Digital-Naturalism-Laboratories/Mothbox/docs/index.md

---
layout: default
title: Home
nav_order: 1
description: "The Mothbox is a low cost DIY insect monitor"
permalink: /
---

# Mothbox
The Mothbox is a low-cost, high-performance [insect monitor](https://digital-naturalism-laboratories.github.io/Mothbox/docs/about/specs/). It features a power efficient and lightweight design that helps field biologists deploy it in the depths of the jungle. Its low cost means you can deploy many devices to study a landscape or build one to study the biodiversity at your home!

All the physical designs, electronics schematics, Pi Scripts, and insect-IDing Artificial Intelligence are **provided free and open source**, so you can build, share, and improve on these designs yourself!

We currently offer designs for two different versions of the Mothbox now:
* [Mothbox Pro](https://digital-naturalism-laboratories.github.io/Mothbox/docs/building/mothbox_pro) - Factory Assembled electronics, easy to put together! (~$450 in parts)
* [Mothbox DIY](https://digital-naturalism-laboratories.github.io/Mothbox/docs/building/mothbox_diy) - Make a Mothbox entirely yourself with off-the-shelf parts! ($550 in parts)

We believe **studying insect biodiversity is integral to life on earth**, and simply want this technology in the hands of as many people as possible.

{: .important-title }
> Mailing List
>
> Are you interested in Mothboxing? Using it in the field? Building it? Please sign up for our mailing list to stay up to date with the latest features! **Email our rag-tag crew at INFO [ a t ] mothbox.org** with subject "Mothbox Mail."
>

{: .highlight }
Join our free [Mothbox CHAT GROUP](https://app.element.io/#/room/#mothbox:matrix.org)

{: .important-title }
> Mailing List
>
> Are you interested in Mothboxing? Using it in the field? Building it? Please sign up for our mailing list to stay up to date with the latest features! **Email our rag-tag crew at INFO [ a t ] mothbox.org** with subject "Mothbox Mail."
>
https://app.element.io/#/room/#mothbox:matrix.org

{: .important-title }
> Order Form
>
> If you want to get your hands on some new Mothboxes ASAP, [fill out our interest form](https://forms.gle/BnBhjBC4csW4BwTE7), and we will get back to you as soon as we can about how to get them to you!
>

See the [full specifications of what it can do here.](https://digital-naturalism-laboratories.github.io/Mothbox/docs/about/specs/)
Watch a [video presentation of our talk at the Smithsonian all about the Mothbox and its design.](https://www.youtube.com/watch?v=lZhh7ecnAgk)
or [read a scientific paper](https://besjournals.onlinelibrary.wiley.com/doi/10.1111/2041-210x.70327) about using a Mothbox!

PXL_20240720_054408351 MP-EDIT



## Why Study Insects for Conservation?
Insect populations can be used as an ultra high resolution sensor for changes in environments.

bafkreic4l337soddqseixdb4zy74mdmzqtg4g7v75toiondz2vouumwnlm-1

### Insects (Especially Moths and Beetles) are Hyperdiverse
Of all life on earth (including bacteria), there are about 2 million species scientists have described, and [half of all those species are insects!](https://ourworldindata.org/how-many-species-are-there#:~:text=In%20the%20chart%2C%20we%20see,reptiles%2C%20and%20over%206%2C000%20mammals.) What's more, if you look at **just moths,** there are about 144,000 species, meaning **about 1 in every 14 known species in the world is a moth!** For reference, there are only about 11,000 bird species, and only 6,500 species of mammals (and half are bats and rodents). 

Using creatures with a super diverse gene pool allows us to make sophisticated insights into the health of different areas. Combining the activity of thousands of species of insects with other data like climate, acoustic, or soil analysis, can provide deep analysis into how damaged environments can be repaired.

### Offer Highly Localized Insights
Because they tend to have short lives and often limited ranges, insects can provide super localized data. Moths, in particular, are great indicators of overall biodiversity, because they are often host-specific as caterpillars. This means they only feed on one or a limited number of plant species. So, by monitoring moths, you are getting proxy information about the local plant community.

For comparison, think about something like a jaguar. Jaguars are rarely spotted and scientifically valuable to see on a wildlife camera, but they have large ranges and long lives. The presence of a jaguar does not necessarily tell us much about the health of the specific environment where it was spotted. It could simply be travelling across disturbed farmland to escape from a destroyed habitat elsewhere, but this would not be an indicator that the disturbed farmland is healthy and safe for jaguars. 

Having an insect sensor (like a Mothbox) that compares the activity of thousands of different species of insects can highlight differences in environmental health in areas just a couple kilometers apart.

### They are Easy to Attract
Humans long ago discovered that many nocturnal insects like moths seem to be attracted to lights. We now know this is because [bright lights disorient their natural steering mechanism](https://www.nature.com/articles/s41467-024-44785-3). Scientists have used bright artificial lights for over a century to take censuses of insect populations. The problem with this type of "mothlighting" is that it can be incredibly time consuming, as a scientist has to hang out with the mothlight all night and note which insects are visiting. Instead we have an automated device that does all this work for you! You just deploy the Mothbox in the field, it runs while you're in the comfort of your own home, and you can collect it and analyze the data with AI when you're ready.

## What it Does

The Mothbox stays in an ultra low-power state until your schedule tells it which nights to wake up. Then it triggers an insect lure (usually a bright UV light) and takes ultra-high resolution photos of the visitors it attracts. 

PXL_20240607_025924783 NIGHT-EDIT

Next we created some open-source AI scripts that process the insect data for you. First, a trained YOLO v8 detects where all the insects are in the images and crops them out. This means that you can view just the cropped photos of insects instead of having to look through all the raw photo data.




Then we use BioCLIP via the [pybioclip](https://github.com/Imageomics/pybioclip) package, with a [FiftyOne](https://github.com/voxel51/fiftyone) user interface, to help you automatically group and ID the insects to different taxonomic levels!



# Build it Yourself!
PXL_20240810_155421647 MP

This Mothbox documentation will provide you with information on how to source, build, program, and use your Mothbox!

[Get started building your mothbox!](https://digital-naturalism-laboratories.github.io/Mothbox/docs/building)

After following these guides, you should be able to make your own set of Mothboxes to conduct your own biodiversity studies!




# Mothbeam
We are also building an open-source, portable, low-cost light for mothlighting, the Mothbeam! Some early documentation for [making your own Mothbeam is here.](https://mothbox.org/docs/building/mothbeam)


PXL_20240718_190826331 MP
