Digital-Naturalism-Laboratories/Mothbox/docs/docs/about/Acknowledgements.md

---
layout: default
title: Acknowledgements
parent: About the Mothbox
has_children: false
nav_order: 9
---
# Development Team

The Mothbox was originally developed by a core team of Andy Quitmeyer, Hubert Szczgiel, and Kitty Quitmeyer

* Andy Quitmeyer

Dr. Andy Quitmeyer designs new ways to interact with the natural world. Quitmeyer has worked with large organizations like Cartoon Network, IDEO, and the Smithsonian, taught as a tenure-track professor, and even had his research turned into a (silly) television series called “Hacking the Wild." distributed by Discovery Networks.

He spends most of his time volunteering with smaller organizations and communities, and co-founded the field-station/makerspace, [Digital Naturalism Laboratories](https://www.dinalab.net/). In the rainforest of Gamboa, Panama, Dinalab blends biological fieldwork and technological crafting with a community of local and international scientists, artists and engineers. 

* Hubert Szczygiel

Hubert Szczygiel is a tropical ecologist specializing in scalable biodiversity monitoring. Hubert has worked with the Smithsonian Tropical Research Institute since 2016. His current research pairs broad-spectrum biodiversity monitoring with new financial tools to enable reforestation. His research inspired the development of the original Mothbox.

* Kit Quitmeyer

Kit Quitmeyer is the Co-founder of [Dinalab](https://www.dinalab.net/), and lead technician of the protoyping facilities. With the Mothbox she has been the head of manufacturing operations and software training. She is a skilled craftsperson passionate about endangered animals, books, activism, and the environment. She works weekly at the [APPC animal rescue in Panama](https://www.appcpanama.org/who-we-are.html), and raises funds with her crafts to support them.

* Bri Johns

Bri Johns is an open science hardware researcher. After her role steering the Gathering for Open Science Hardware group as the community manager, she joined the Mothbox team as a research fellow working on the construction, deployment, and community access for the tool.

# Acknowledgements
The Mothbox has been made possibly with help from many individuals and groups like 

## Funding
* Wildlabs.net
* ARM
* The American Museum of Natural History
* Experiment.com
* Phoebe Zarnetske and the Michigan X-prize group

## Institutional Support

* [IVADO Institute](https://ivado.ca/)
  * Sponsored a collaboration with us and [Antenna](https://antenna.insectai.org) software for processing bugs
* Autodesk Foundation (Software Donation)
* University of Washington (Project Storage Space)

## Additional Support

* Pro-Eco Azuero
* Ponterra

* Daisy Dent
* Yash Sondhi
* Owen Mcmillan
* Sol Parra Santos

* [Craig Durkin](https://wandrer.earth/) set up this documentation site backend for us

* Christopher Lawrence
* GOSH community openhardware.science
* Lee Wilkins
* Julian Stirling
* Wildlives Rhode Island group
* Matt Flagg

* David Rolnick's lab and the [Antenna](https://antenna.insectai.org) crew

* Totumas Crew
 * Jessie Tejara-Fabian
 * Jeff Dietrich
 * Mulget Amaru
* [BeetlePalooza](https://doi.org/10.5281/zenodo.15272136) (Sponsored by the [Imageomics Institute](https://imageomics.org/) at The Ohio State University)
* [Bucket of Bugs](https://github.com/Digital-Naturalism-Laboratories/bucket-o-bugs) BeetlePalooza group
  * Elizabeth Campolongo, Ernie Parke, Andy Quitmeyer, Matt Thompson
* The McGuire Center for Lepidoptery

* Epaper Display Font help:
  * Logan Williams and Linotype Pilgrim 

* PCB Assistance
  * Paul Parkview 
  * Josh Muffin
  * Joel Murphy

* [TroubleMaker Shenzhen](https://troublemaker.site/)
  * Henk, Terry, and Ming
