Digital-Naturalism-Laboratories/Mothbox/docs/docs/processing/index.md

---
layout: default
title: Refining Data
nav_order: 4
has_children: true
permalink: /docs/processing
---
Have you been using the Mothbox, and now you have thousands of photos of cool bugs!? Want to do neat things with all these photos to turn them into interesting and beautiful data? We built a suite of open source scripts that we call the "Mothbot" for Mothbox! Check them all out!

There are two stages we go through to turn all our raw data into useful insights. We group them into

* Process - Mostly automated steps turning source images into labeled sub images
  * image(3)

* Classify - Augmented Human validation of insect data
  * image(4)
