Digital-Naturalism-Laboratories/Mothbox/docs/docs/previousversions/v3.21/3.21.md

---
layout: default
title: v3.21
nav_order: 9
has_children: true
permalink: /docs/previousversions/v3.21

---

# v3.21

This version was put into the field in April 2024. It features a pi 4 + pijuice + USB buck converter. It had multiple internal planes.
