Digital-Naturalism-Laboratories/Mothbox/docs/docs/processing/process/hacker/id.md

---
layout: default
title: Identify Detections
parent: Hacker Mode
has_children: false
nav_order: 4
---

## Using the Mothbot UI to ID Organisms

The next step in the data processing pipeline is to run a script that identifies all the organisms that were detected in the previous step. You can start by clicking on the tab that says "ID" towards the bottom of the UI. 

mothbotID1<br>

Once you've clicked this tab, you will notice a few new fields that pop up. The first field is the option to set the parameters for the taxonomic rank that the computer vision model ([BioCLIP](https://imageomics.github.io/bioclip/)) will use when identifying organisms (i.e. whether you want the model to identify your organisms to just the order level, or all the way down to the species level).

On the right side, you will see checkboxes to identify human and bot detections. You should leave both of these as true, as this will ensure every detection gets identified. You also have the option to override existing IDs if you would like by selecting the last checkbox.

MothbotID2<br>

Click the big orange box that says "Run Identification" and you will see the script running in the window below it.

MothbotID3<br>

> [!NOTE]
> When you first run the ID program with a specific species list, it needs to do a thing where it creates "embeddings" of that specific species list. They get saved as a ".pt" file next to your species list. This means the first time you run an ID, it might take a bit longer, but subsequent ID processing with the same species list should go faster! HOWEVER, there can be a time where, if you update that species list, you can get an error when you run the script because the old embeddings don't match that species list. so **if you get an error, delete that ".pt" file, and run it again**

When you are done running the ID script, your window should look like this (notice the green checkbox indicating that identifications are complete and text that says identification process is complete):

IDfinished<br>

## Next: Insert Metadata
Now that you have detected and identified your organisms, the next step is to make sure the metadata for your deployment is associated to your identified organisms. Head to the next step “[Insert Metadata](https://digital-naturalism-laboratories.github.io/Mothbox/docs/processing/process/hacker/insertmetadata/)” to continue.

## Run this Script Manually

The Python Script we use to run detections is called Mothbot_ID. This script tries to look at all your detected creatures and make a prediction as to what type of creature they are.

# Inputs
Like many of the other processing scripts, this program takes in several Inputs as default variables that you can change at the top of the file.


INPUT_PATH  - set this to the folder you want to ID (or a parent folder for a group of nights you want to ID).

SPECIES_LIST - path to a CSV file downloaded from GBIF's species list generator. For example, you could download this list of [only the insects that are in Panama](https://www.gbif.org/occurrence/taxonomy?country=PA&taxon_key=216). 

TAXONOMIC_RANK_FILTER=Rank.ORDER
This is the filter where you determine how deep you want the detections to go. The default is set to Rank.ORDER to try to determine what the ID of the creature is down to the ORDER level. You can change this all the way until Rank.SPECIES, but the accuracy of the AI model falls off the deeper you get. 
_Generally the Rank.ORDER or Rank.Family level are the most usuable settings_

# Results
The ID script can take 10-90 minutes depending on your computer speed and number of detections.

When you run the script, you will see it start processing your detections in each image.


It chooses a winning classification down to the taxonomic filter you specified (for example Order).
It saves this detection information into the .json files that you created when manually making detections or running the automated Detect script. (So you won't see any new files created.)

Now if you open your nightly folder in X-Anylabeling, you will see the labels no longer just say "creature" but rather list the taxonomic rank the script has predicted:





For editing and organizing these IDs into a dataset, we will go to the next step where we view all our results in an editable database.
