Digital-Naturalism-Laboratories/Mothbox/docs/docs/processing/process/hacker/insertExif.md

---
layout: default
title: Exif (Optional)
parent: Hacker Mode
has_children: false
nav_order: 7
---
# Launch Exif (Optional)

## Make Sure Exiftool is installed
There is a thing called "ExifTool" that (because exif data on images is super convoluted) needs to be installed to run CreateDataset


if you are using windows, you don't actually have to install it i think. It just points to a relatively positioned folder in the github that has the .exe it runs
if you are running mac or linux, you need to download exiftool (or the mac package .pkg is actually in in the AI folder of the github already for you as well)

## Insert EXIF Data Using Mothbot UI

We've created a script to insert EXIF data into each patch you've made, which is useful when you want to upload individual patches as photos to crowdsourcing platforms like iNaturalist. You can do this by clicking on the "Insert Exif" tab, then clicking the big orange button that says "Insert Exif"

exif1<br>

Once your script is running, it should look like this:

exif2<br>

And when it's finished, your window at the bottom should look like this:

exif3

You can now head to the next step, [Generating and Editing Datasets](https://digital-naturalism-laboratories.github.io/Mothbox/docs/processing/classify/)!
