Digital-Naturalism-Laboratories/Mothbox/docs/docs/about/index.md

---
layout: default
title: About the Mothbox
nav_order: 10
has_children: true
permalink: /docs/about
---

This is an open source science hardware and software project started by Andy Quitmeyer and Hubert Szczygiel in 2023. The goal is to provide people a low cost tool for insect biomonitoring they can build themselves from off the shelf parts. It aims to be low cost, high resolution, durable, and portable.

# Publications

You can read papers we published about the Mothbox here:

* [Methods in Ecology and Evolution](https://besjournals.onlinelibrary.wiley.com/doi/epdf/10.1111/2041-210x.70327) preprint [here](https://www.biorxiv.org/content/10.64898/2025.12.03.692171v2)
* [Integrative and Comparative Biology](https://academic.oup.com/icb/advance-article/doi/10.1093/icb/icag072/8700641?guestAccessKey=)

Here are some other papers published that talk about the Mothbox:

# Video Presentations
Here are some video presentations that discuss the motivations behind the Mothbox and its design:

Documentary about the Mothbox made for the Wildlabs Award:

<iframe width="560" height="315" src="https://www.youtube.com/watch?v=1LGz3aWpeVE&t=102s" title="Mothbox Wildlabs Documentary" frameborder="0" allow="accelerometer; autoplay; clipboard-write; encrypted-media; gyroscope; picture-in-picture; web-share" referrerpolicy="strict-origin-when-cross-origin" allowfullscreen></iframe>

Mothbox Invited Talk at the Smithsonian Tropical Research Institute (September 2024):
<iframe width="560" height="315" src="https://www.youtube.com/embed/lZhh7ecnAgk?si=vdF98dbD3mXoOiNE" title="YouTube video player" frameborder="0" allow="accelerometer; autoplay; clipboard-write; encrypted-media; gyroscope; picture-in-picture; web-share" referrerpolicy="strict-origin-when-cross-origin" allowfullscreen></iframe>

[Mothbox Symposium Keynote at Georgia Tech (October 2024)](https://research.gatech.edu/ipat/mothbox-lecture-oct29-2024)

[Mothbox Invited Seminar: “Expanding Horizons in Lepidoptera Research” McGuire Center Webinar Series ](https://ufl.zoom.us/rec/play/-Vr3mgX_anxGzv7Nv5OYsDCAKpSgtci48Wpri2sOOH7cdTbaxnvzdFAKVjW492BDWsz-Dkzi-UxSENHV.rh4Ph3Je4udUjZ9s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)
