Digital-Naturalism-Laboratories/Mothbox/docs/docs/processing/classify/index.md

---
layout: default
parent: Refining Data
title: Classification
nav_order: 8
has_children: true
permalink: /docs/processing/classify
---
During the classification step, we want to take automatically organized insect data and validate them with humans as quickly and accuratley as possible. We built our own program to let you do this in a quick and speedy way called "Classify."

* [Classify](https://mothbox.org/docs/processing/classify/classify/)

Note: we used to have an older version of this that used a fiftyone UI interface, but switched to this new homebrewed one we call "Classify" as it is much speedier and easier to use.
