Digital-Naturalism-Laboratories/Mothbox/docs/docs/processing/process/hacker/ui.md

---
layout: default
title: Start UI
parent: Hacker Mode
has_children: false
nav_order: 2
---
# Launch Mothbot_UI.py script

This script enables you to run all our post-processing scripts through a web application that runs locally on your computer. We were able to build this interactive user interface (UI) using [Gradio](https://github.com/gradio-app/gradio), an open source Python package that allows anyone to quickly build a web application for any sort of machine learning model or Python functions.  

## Make sure you have the latest version of the Mothbox Project on GitHub
Before running your post-processing scripts, it's important to make sure you have the most recent version of our scripts. You can do this by opening your GitHub desktop application and clicking "Fetch Origin" and then "Pull Origin." This will sync your local Mothbox folder with the repository that has the updated code. 

Github_Fetch<br>

Github_Pull<br>

>Note: if no changes have been made to our scripts, then you likely will not see an option to "Pull Origin" after you fetch it, as there will be nothing new for you to pull. 

Now that you've got the updated scripts, you can proceed with opening the Mothbox UI.

## Opening the UI Using Visual Studio Code

To get the UI running, you need to first open the Mothbot folder in Visual Studio Code. Start by opening your Visual Studio Code app, clicking File, then Open Folder, and opening the Mothbot Folder, which is within the AI folder of the Mothbox project (which can be found in your GitHub folder on your computer).

OpenFolder_VSC<br>
SelectMothbot<br>

You should then see the Mothbot folder appear in the sidebar in Visual Studio Code. Click on the dropdown, then select the Mothbot_UI.py script

mothbotUIinsidebar<br>

You will see the code pop up in the main window of Visual Studio Code, and all you have to do next is click the play button in the top right corner (aka Run Python File).

runpythonfile<br>

Next, the Mothbot UI should pop up as a web application that is running locally on your computer! 

mothbotAI<br>

## Start Detecting Bugs!
Now that you've got the UI running, you can start processing your data by detecting what critters are in your photos. Move on to the next step, Detect Creatures, to learn how!

## Running Scripts Manually
If you would like to run all of our Python scripts manually, we are including instructions on how to do so as part of each post-processing step listed on our site.
