Digital-Naturalism-Laboratories/Mothbox/AI/trained_models/train14_3000Images_batch2_1408px/train_batch67502.jpg

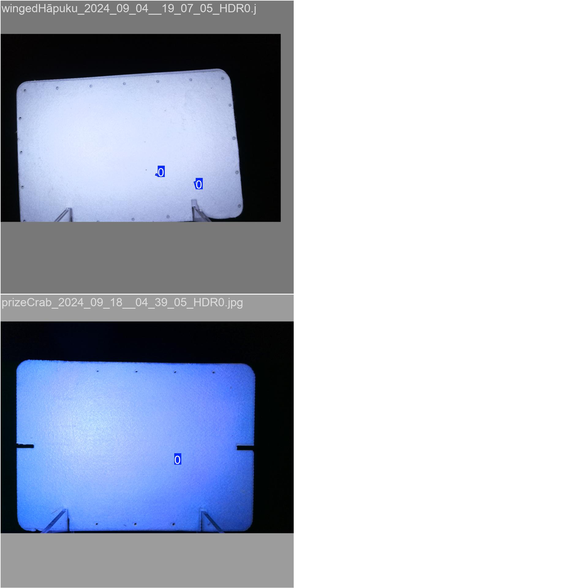
AI/trained_models/train14_3000Images_batch2_1408px/train_batch67502.jpg
