Digital-Naturalism-Laboratories/Mothbox/AI/trained_models/yolo11m_4500_imgsz1600_b1_2024-01-18/train_batch197550.jpg

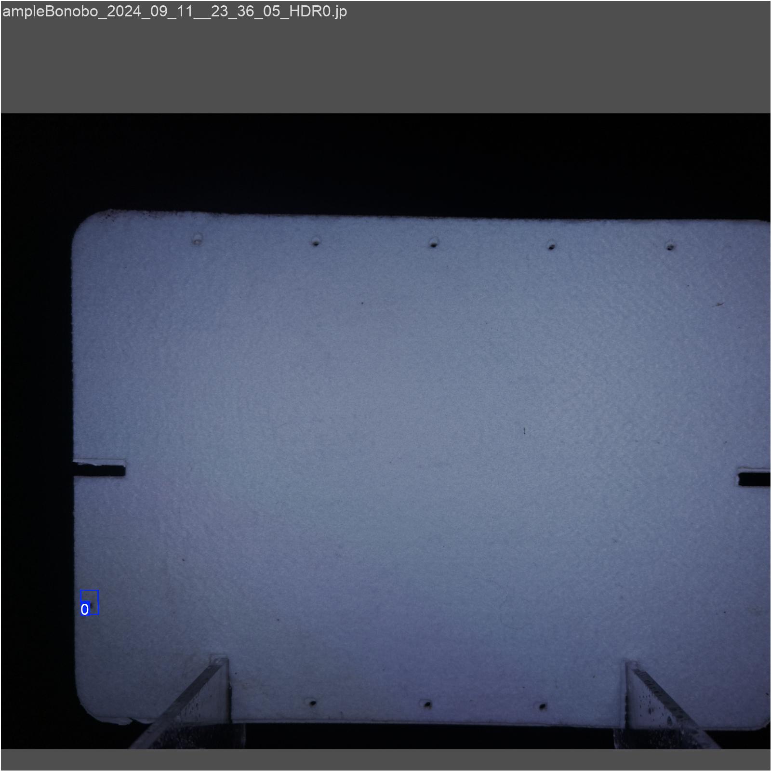
AI/trained_models/yolo11m_4500_imgsz1600_b1_2024-01-18/train_batch197550.jpg
