Digital-Naturalism-Laboratories/Mothbox/AI/visualization_scripts/packed_into_shape.png

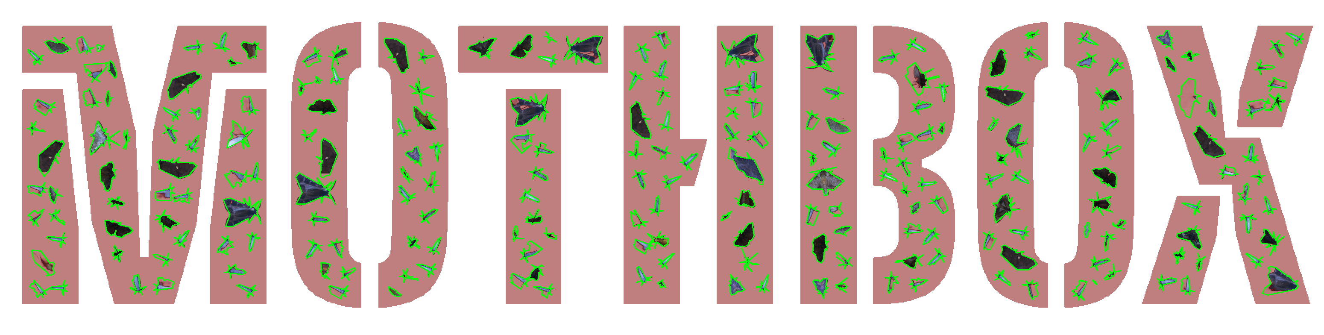
AI/visualization_scripts/packed_into_shape.png
