Digital-Naturalism-Laboratories/Mothbox/docs/graphic_design/croptext.png

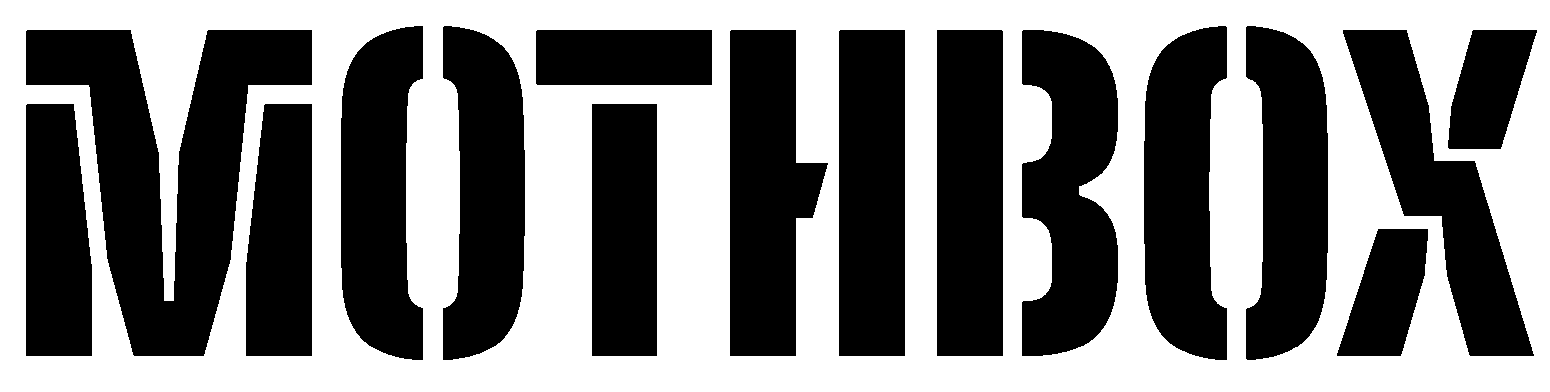
docs/graphic_design/croptext.png
