Digital-Naturalism-Laboratories/Mothbox/docs/graphic_design/cybermothwide4.0.jpg

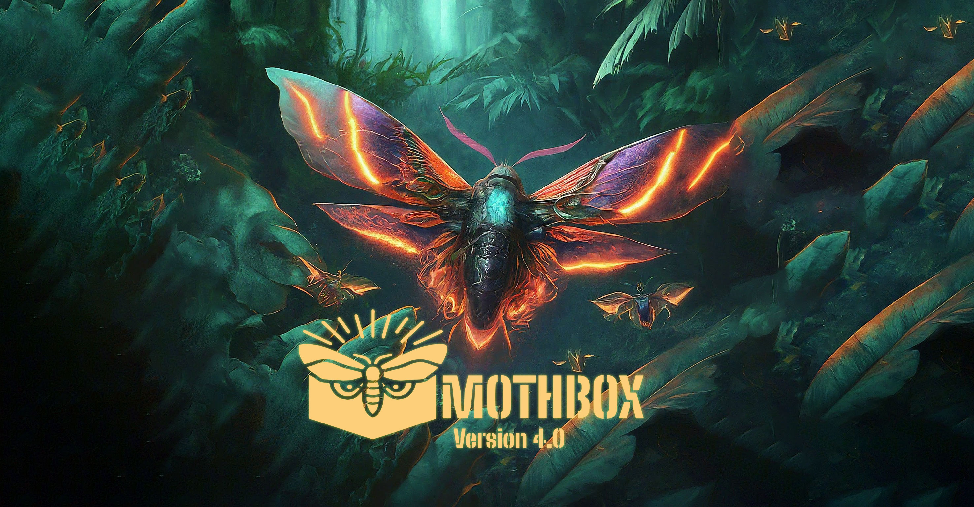
docs/graphic_design/cybermothwide4.0.jpg
