Digital-Naturalism-Laboratories/Mothbox/docs/graphic_design/cybermothwide.jpg

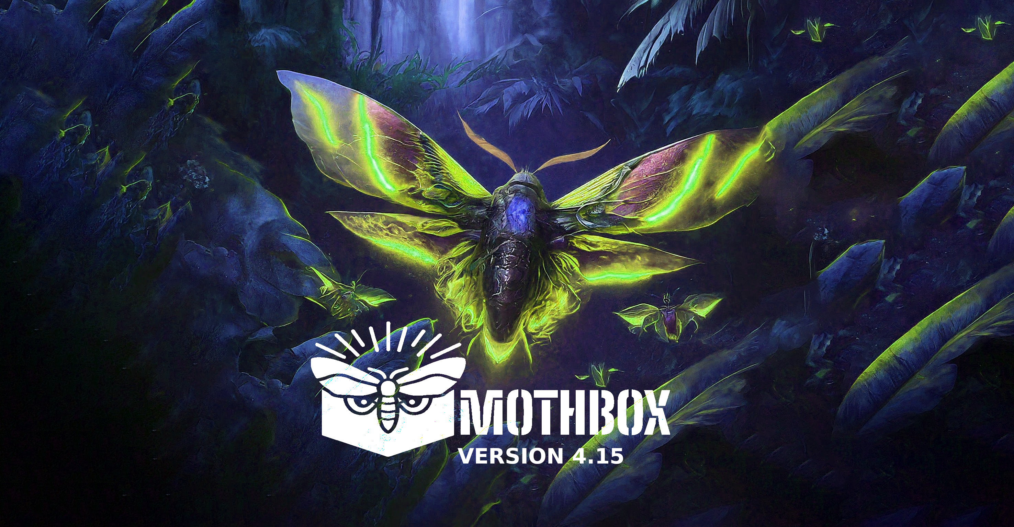
docs/graphic_design/cybermothwide.jpg
