Digital-Naturalism-Laboratories/Mothbox/docs/docs/building/mothbox_pro/assembleincase.md

---
layout: default
title: Assemble in Case
parent: Mothbox Pro
#has_children: true
nav_order: 4
---
Our Mothbox electronics are together, but now we probably need to give it a housing to protect it!


# Determine your Case

You now have two options for housing your Mothbox Pro.

## Off the Shelf
It's compatible with the old hacked Plano fishing box case. 
You can follow instructions for [how to build an off-the-shelf case here](https://digital-naturalism-laboratories.github.io/Mothbox/docs/building/external_parts/case_ots/).

## 3D Print

Better yet, though, you can now 3D print your own cases even cheaper and easier! Follow the instructions for [making a 3D printed case here](https://digital-naturalism-laboratories.github.io/Mothbox/docs/building/external_parts/case_print/).

**The following instructions will be for the 3D printed case option.**

# Prep Chassis
First we need to snip this tiny support piece off the chassis. This section is just there to make printing easier, and we need to remove it so it doesn't get blocked by the case's plugs.




# Screw PCB to Chassis
Place the Mothbox electronics into the chassis.


Make sure the indent in the PCB lines up with the cutout at the bottom of the chassis.


Using #6 x 3/8in long screws (doesn't have to be super exact, something about that size will work), attach the PCB to the inner chassis.


There are 4 holes in the 4 corners of the board. Simply screw them snugly into place.




Everything should feel secure inside this little removable box now!


{: .note }
> Zip tie hack!
> Did you accidentally cover a screw hole? Couldn't find the right size screws in berlin? Use zip ties! We will add better holes for just zipping everything in future PCBs but for now, you can use these hacks:









# Load Chassis into Shell

{: .note }
> Important! Make sure you have [completed putting together the Outershell of your mothbox](https://digital-naturalism-laboratories.github.io/Mothbox/docs/building/external_parts/case_print/) before proceeding!

## Connect the Charge Port to a DC Plug
Use a lever nut and connect a DC Barrel Plug to the wires coming from the charging port of the box. It's useful to do this now, as it will make the cable easier to slide through the chassis.





## Feed Cable Through Notch in PCB

Now send that cable through the little notch in the PCB.


Pull this cable through and slide the chassis with the electronics into the back of the case. 



Make sure the battery area is towards the bottom where the wires from the external sockets are.

## Connect to the Battery's In port
Plug this wire into the "In" port on your battery



You can double check that your wiring is good by plugging the external charger into the bottom of the box and seeing if the light on the charger changes to red (indicating it's charging).


## Connect the External Attractor Port (Optional)
You can hook up your external attractor port to the PCB quite easily.

Take the two ends from the external attractor port, and connect them to the socket box on the back left of the PCB labeled "external attractor"


Make sure 
* the black wire goes to a negative "-" port
* the red wire goes to a positive "+" port


# Tidying Up Wires (Optional)
This is optional, but I like to add a little piece of tape to keep the camera cable from getting in the way.


# Connect Back Lid
Your Mothbox should be fully functional now!

You can close it up now by putting the back lid on. 


You can use a variety of closures to attach the lid:

* 1/4 in bolts and nuts
* Reusuable zip ties
* or (my favorite) rubbery silicone ties


# Congrats on your Mothbox!
You made one! It's beautiful!
