Digital-Naturalism-Laboratories/Mothbox/docs/docs/building/mothbox_pro/v5.0.3/index.md

---
layout: default
title: v5.0.3
parent: Mothbox Pro
grand_parent: Building
nav_order: 1
has_children: true
permalink: /docs/building/mothbox_pro/v5.0.3/
---

# Mothbox Pro v5.0.0 - v5.0.5

These are the build instructions for versions of the Mothbox with **PCB mainboards labeled v5.0.0-v5.0.5**, (the previous version of the Mothbox Pro hardware made between 2025-September 2026). These have been tried and tested in the field, but newer versions have a couple tweaks to make an easier build based on this field testing. 

If you have a v5.0.6 board, head over to the [v5.0.6 instructions](https://digital-naturalism-laboratories.github.io/Mothbox/docs/building/mothbox_pro/v5.0.6) instead.

Work through the steps below in order:
