Digital-Naturalism-Laboratories/Mothbox/docs/docs/previousversions/v3/building/building.md

---
layout: default
title: Building Mothbox
nav_order: 3
has_children: true
permalink: /docs/previousversions/v3/building
---

# Assembly
This guide will show you how to construct a mothbox from scratch!
