Digital-Naturalism-Laboratories/Mothbox/docs/docs/building/mothbox_pro/v5.0.6/index.md

---
layout: default
title: v5.0.6
parent: Mothbox Pro
grand_parent: Building
nav_order: 1
has_children: true
permalink: /docs/building/mothbox_pro/v5.0.6/
---

# Mothbox Pro v5.0.6

Work through the steps below in order:
