Digital-Naturalism-Laboratories/Mothbox/docs/docs/previousversions/v3/usage/using.md

---
layout: default
title: Using Mothbox
nav_order: 2
has_children: true
permalink: /docs/previousversions/v3/using
---

# Using the Mothbox

This will contain pages detailing how to use the mothbox
