Digital-Naturalism-Laboratories/Mothbox/docs/Quick Reference Guide/linkedimgs/1D35AEB0.jpg

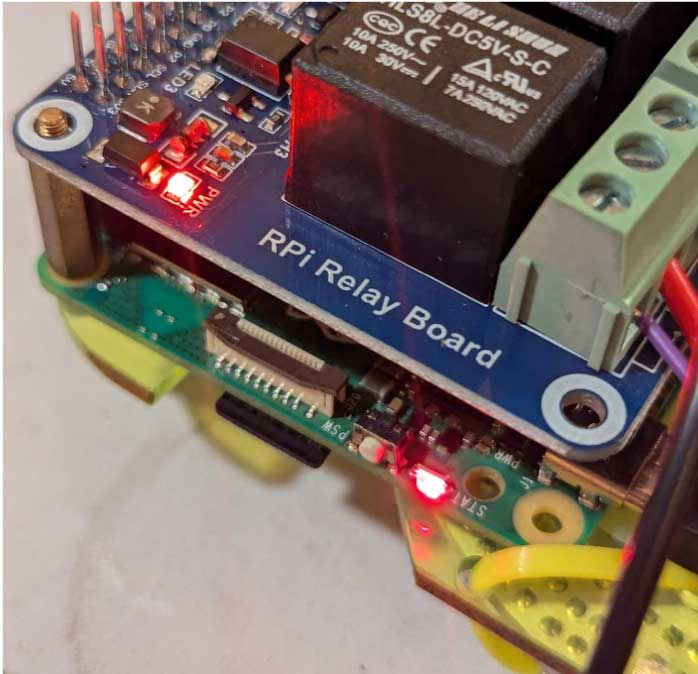
docs/Quick Reference Guide/linkedimgs/1D35AEB0.jpg
