Digital-Naturalism-Laboratories/Mothbox/docs/Quick Reference Guide/linkedimgs/1D35AECE.jpg

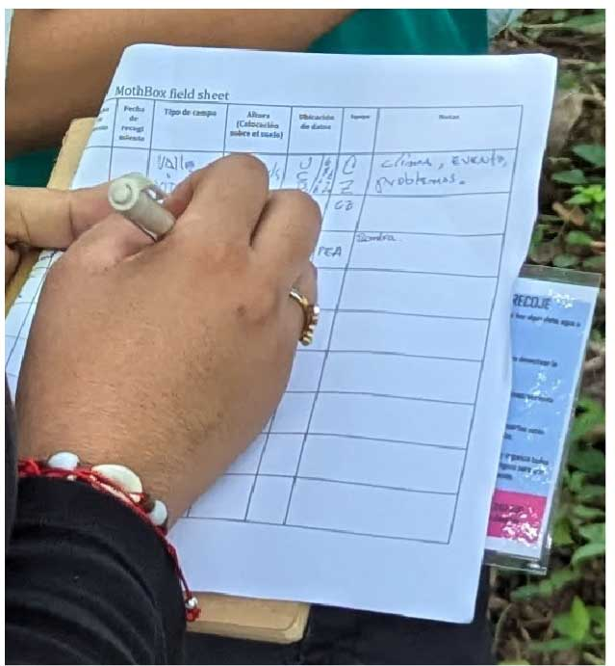
docs/Quick Reference Guide/linkedimgs/1D35AECE.jpg
