Digital-Naturalism-Laboratories/Mothbox/docs/Quick Reference Guide/linkedimgs/1D35AED0.png

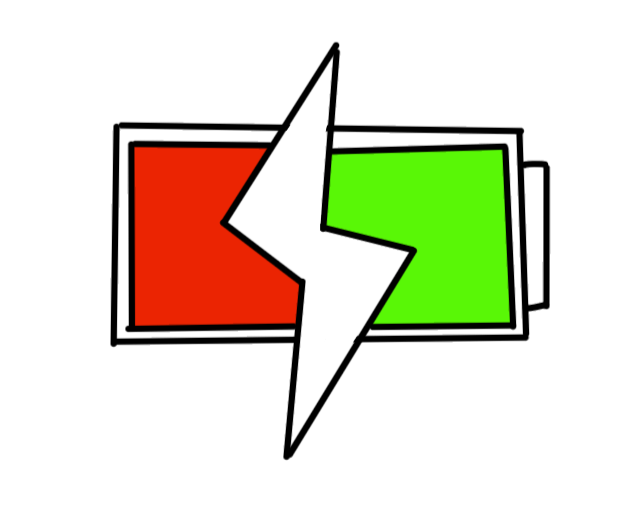
docs/Quick Reference Guide/linkedimgs/1D35AED0.png
