Digital-Naturalism-Laboratories/Mothbox/docs/Quick Reference Guide/linkedimgs/3E4E0CC1.png

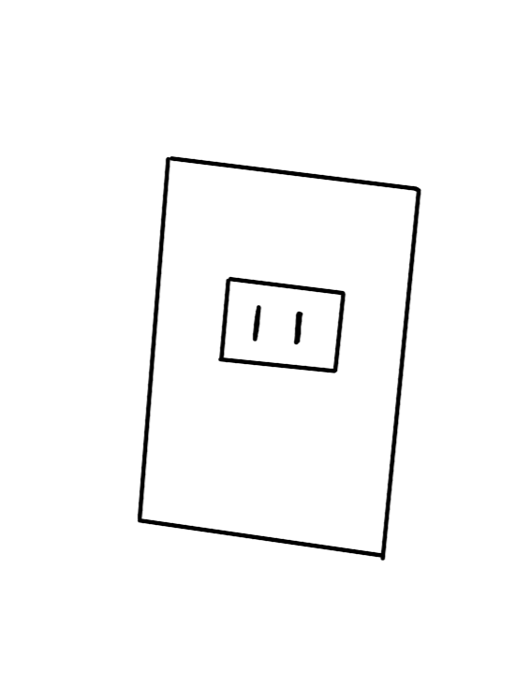
docs/Quick Reference Guide/linkedimgs/3E4E0CC1.png
