Digital-Naturalism-Laboratories/Mothbox/docs/Quick Reference Guide/linkedimgs/147DD7A.jpg

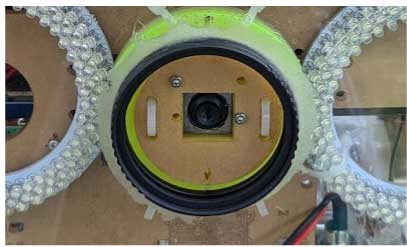
docs/Quick Reference Guide/linkedimgs/147DD7A.jpg
