Digital-Naturalism-Laboratories/Mothbox/docs/Quick Reference Guide/Mothbox_Quick_ReferenceGuide_v3BigText_English.png

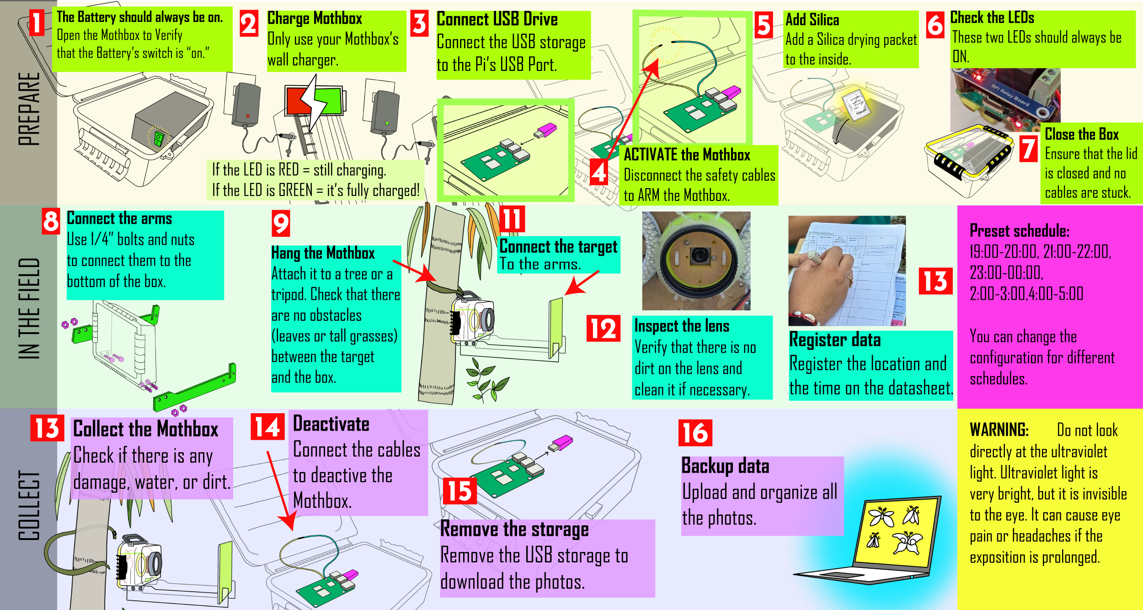
docs/Quick Reference Guide/Mothbox_Quick_ReferenceGuide_v3BigText_English.png
