Digital-Naturalism-Laboratories/Mothbox/docs/Quick Reference Guide/Mothbox_Quick_ReferenceGuide_v3BigText_ESP.png

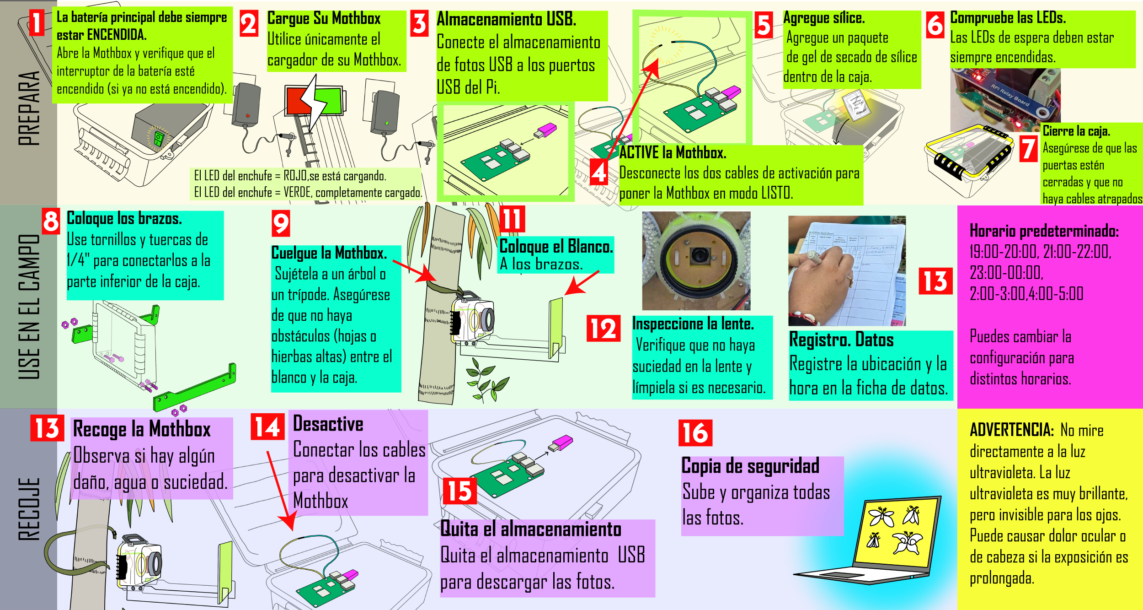
docs/Quick Reference Guide/Mothbox_Quick_ReferenceGuide_v3BigText_ESP.png
