Digital-Naturalism-Laboratories/Mothbox/AI/visualization_scripts/packed_result.png

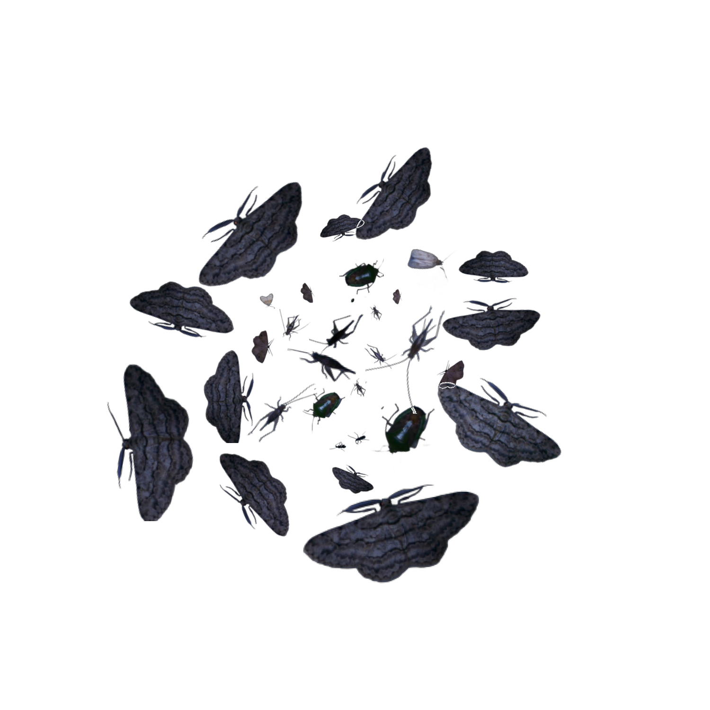
AI/visualization_scripts/packed_result.png
